hexmaster111/TI92-SBC-DOCK/CM4/TP4056-Lithium-Ion-Battery-Charger-Circuit-Diagram.jpg

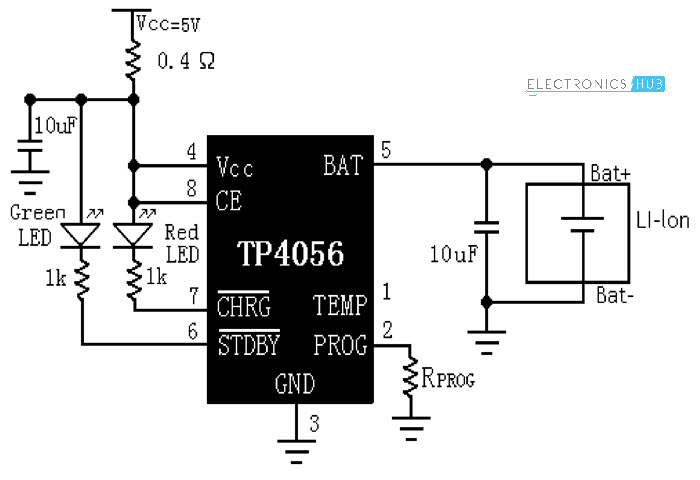
CM4/TP4056-Lithium-Ion-Battery-Charger-Circuit-Diagram.jpg
